edofullin/esp32-devboard-clima/spice/TermostatoOT.asc

D1: diode; 1N4148
D2: diode; 1N4148
D3: diode; 1N4148
D4: diode; 1N4148
D5: zener; 1N750
D6: zener; BZX84C15L
D7: zener; 1N750
I1: current; PULSE(6m 17m 0 0 0 5m 10m)
M1: pmos; AO3423
R1: res; 330
R2: res; 220
R3: res; 100
R4: res; 100
R5: res; 330
R6: res; 10k
TX: voltage; PULSE(0 3.3 0 0 0 5m 10m)
U1: PC817A
U2: PC817A
V1: voltage; 24
V3: voltage; 3.3
Named nets: 0, RX, OT1, OT2
.tran 100m
